luqas11/configurable-timed-relay/circuit/circuit.kicad_sch

## KiCad design circuit/circuit.kicad_sch (2025-03-28, an earlier design)

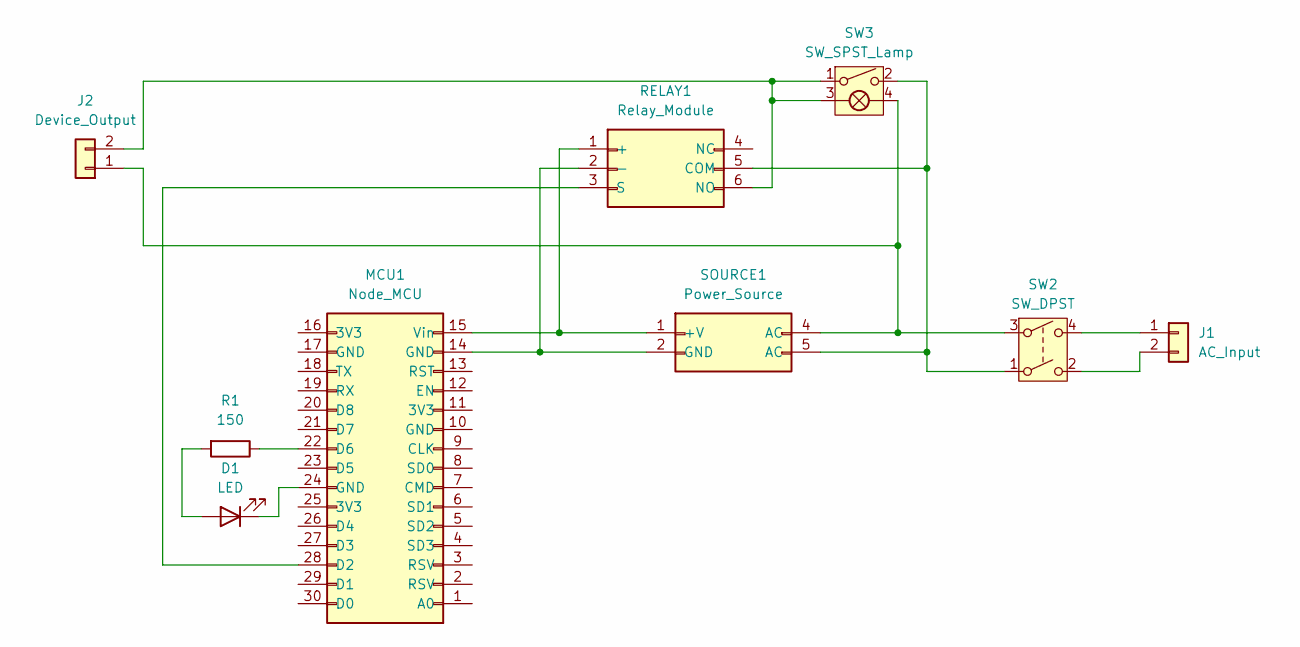
[picture p9: schematic circuit.kicad_sch]

Parts:
D1: LED
J1: AC_Input
J2: Device_Output
MCU1: Node_MCU
R1: 150
RELAY1: Relay_Module
SOURCE1: Power_Source
SW2: SW_DPST
SW3: SW_SPST_Lamp

Connections:
unnamed: D1.1 (K), MCU1.24 (GND)
unnamed: D1.2 (A), R1.2
unnamed: J1.1, SW2.4
unnamed: J1.2, SW2.2
unnamed: J2.1, SOURCE1.4 (AC), SW2.3, SW3.4 (L)
unnamed: J2.2, RELAY1.6 (NO), SW3.1, SW3.3 (L)
unnamed: MCU1.14 (GND), RELAY1.2 (-), SOURCE1.2 (GND)
unnamed: MCU1.15 (Vin), RELAY1.1 (+), SOURCE1.1 (+V)
unnamed: MCU1.22 (D6), R1.1
unnamed: MCU1.28 (D2), RELAY1.3 (S)
unnamed: RELAY1.5 (COM), SOURCE1.5 (AC), SW2.1, SW3.2
