luqas11/configurable-timed-relay/firmware/TimeUtils.cpp

#include "TimeUtils.h"
#include <ESP8266WiFi.h>
#include <TimeLib.h>
#include <WiFiUdp.h>

static const char ntpServerName[] = "us.pool.ntp.org";
const int timeZone = -3;

WiFiUDP Udp;
unsigned int localPort = 8888;

const int NTP_PACKET_SIZE = 48;
byte packetBuffer[NTP_PACKET_SIZE];

time_t getNtpTime() {
  IPAddress ntpServerIP;

  while (Udp.parsePacket() > 0)
    ;
  WiFi.hostByName(ntpServerName, ntpServerIP);
  memset(packetBuffer, 0, NTP_PACKET_SIZE);
  packetBuffer[0] = 0b11100011;
  packetBuffer[1] = 0;
  packetBuffer[2] = 6;
  packetBuffer[3] = 0xEC;
  packetBuffer[12] = 49;
  packetBuffer[13] = 0x4E;
  packetBuffer[14] = 49;
  packetBuffer[15] = 52;
  Udp.beginPacket(ntpServerIP, 123);
  Udp.write(packetBuffer, NTP_PACKET_SIZE);
  Udp.endPacket();
  uint32_t beginWait = millis();
  while (millis() - beginWait < 1500) {
    int size = Udp.parsePacket();
    if (size >= NTP_PACKET_SIZE) {
      Udp.read(packetBuffer, NTP_PACKET_SIZE);
      unsigned long secsSince1900;
      secsSince1900 = (unsigned long)packetBuffer[40] << 24;
      secsSince1900 |= (unsigned long)packetBuffer[41] << 16;
      secsSince1900 |= (unsigned long)packetBuffer[42] << 8;
      secsSince1900 |= (unsigned long)packetBuffer[43];
      return secsSince1900 - 2208988800UL + timeZone * SECS_PER_HOUR;
    }
  }
  return 0;
}

void beginTime() {
  Udp.begin(localPort);
  setSyncProvider(getNtpTime);
  setSyncInterval(300);
}

void forceTimeSync() {
  setSyncProvider(getNtpTime);
}

bool isTimeSet() {
  return timeStatus() != timeNotSet;
}

uint16_t getCurrentHour() {
  return hour();
}

uint16_t getCurrentMinute() {
  return minute();
}
